mattack65/led-mini-lamp/photos/IMG_4350.jpg

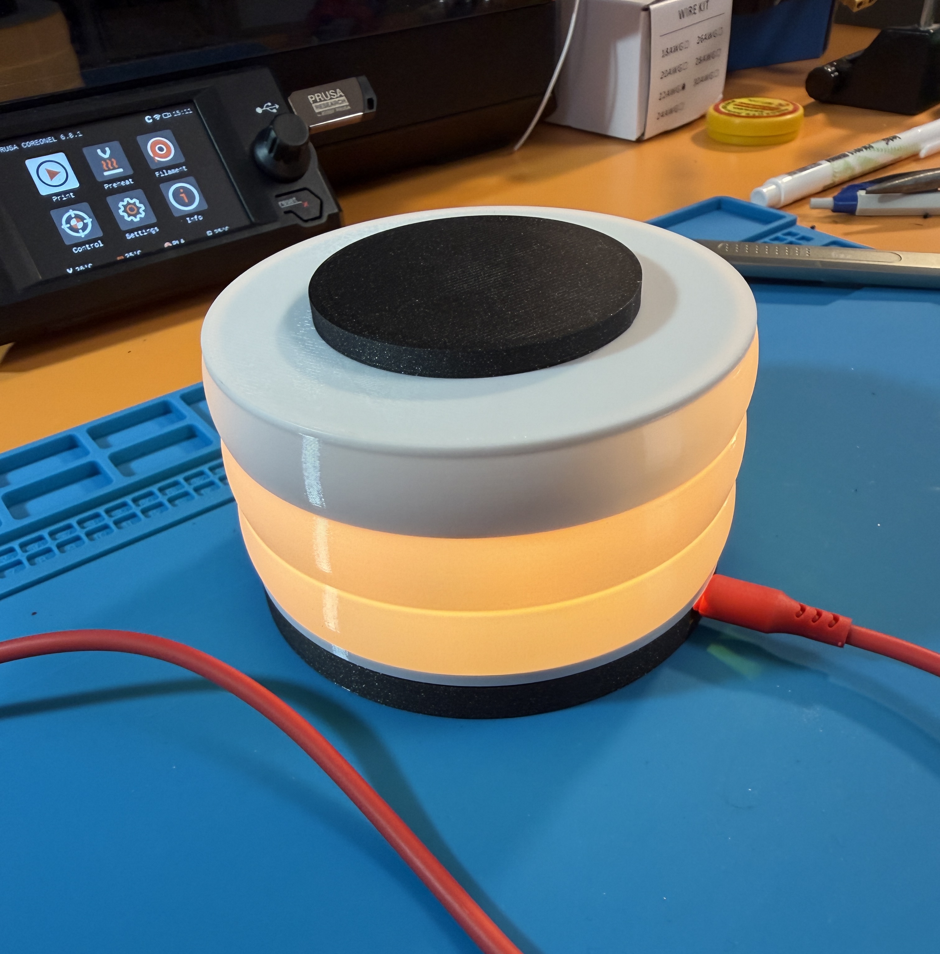
photos/IMG_4350.jpg
