mattack65/led-mini-lamp/photos/IMG_4355.jpg

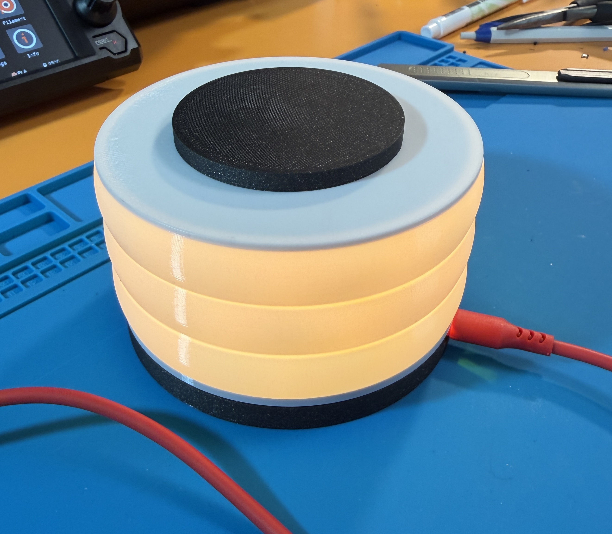
photos/IMG_4355.jpg
